IceForgTW/retr3d/docs/macro/step1.png

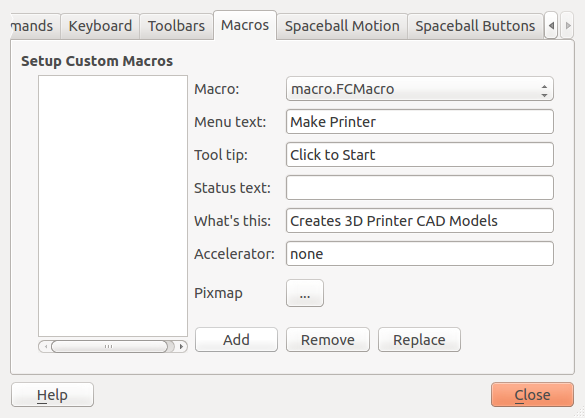
docs/macro/step1.png
